rich-dobbs-13440/chromatofore/src/inchworm/filament_clamp.scad

include <ScadStoicheia/centerable.scad>
use <ScadStoicheia/visualization.scad>
include <ScadApotheka/material_colors.scad>
include <ScadApotheka/m2_helper.scad>
include <nutsnbolts-master/cyl_head_bolt.scad>
include <nutsnbolts-master/data-metric_cyl_head_bolts.scad>
use <PolyGear/PolyGear.scad>


a_lot = 200;
d_filament = 1.75 + 0.;
od_ptfe_tube = 4 + 0;
id_ptfe_tube = 2 + 0;


NEW_DEVELOPMENT = 0 + 0;
DESIGNING = 1 + 0;
MESHING_GEARS = 2 + 0;
ASSEMBLE_SUBCOMPONENTS = 3 + 0;
PRINTING = 4 + 0;



/* [Output Control] */

mode = 0; // [0:"New development, hide other parts", 1:"Designing, no rotation or translation", 2:"Meshing gears", 3: "assembly", 4: "Printing"]

function layout_from_mode(mode) = 
    mode == NEW_DEVELOPMENT ? "hidden" :
    mode == DESIGNING ? "as_designed" :
    mode == MESHING_GEARS ? "mesh_gears" :
    mode == ASSEMBLE_SUBCOMPONENTS ? "assemble" :
    mode == PRINTING ? "printing" :
    "unknown";
    
show_parts = true;
show_vitamins = true;
show_filament = true;
hide_sample_gear_keys = true;

traveller_body_visibility = 1; // [1:Solid, 0.25:Ghostly, 0:"Invisible, won't print" ]
gear_holder_visibility = 1; // [1:Solid, 0.25:Ghostly, 0:"Invisible, won't print" ]
clamp_gear_visibility = 1; // [1:Solid, 0.25:Ghostly, 0:"Invisible, won't print" ]
clamp_slot_gear_visibility = 1; // [1:Solid, 0.25:Ghostly, 0:"Invisible, won't print" ]
small_bevel_gear_visibility = 1; // [1:Solid, 0.25:Ghostly, 0:"Invisible, won't print" ]
big_bevel_gear_visibility = 1; // [1:Solid, 0.25:Ghostly, 0:"Invisible, won't print" ] 
gear_mesh_keys_visibility = 1; // [1:Solid, 0.25:Ghostly, 0:"Invisible, won't print" ]




slide_length = 50; // [1 : 1 : 99.9]
screw_lift = 0; // [-.1 : .1 : 1]

/* [Design] */

print_clearance = 0.1; // Just making it enough that Mesh tools can separate parts
x_clamp_nut_block = 7;
n_teeth_small = 9; // [9, 10, 11]




/* [Clamp Gearing Design] */
clamp_gear_height = 8;
h_bottom_clamp_gear = 1;
clamp_gear_module = 1;
ptfe_insert_clearance = 0.2;


/* [Bevel Gearing Design] */

bevel_gear_module = 1.5; //[1:0.1:2]
small_bevel_gear_cone_angle = 45; // [-90:90]
small_gear_tooth_width = 6; // [0 : 20]
dz_small_bevel_gear = 7.4; // [7:0.1: 9]
dz_shaft_small_bevel_gear = 0; // [-5:0.1:5]
h_small_bevel_shaft = 2; // [0:40]
l_bevel_shaft_bearing = 10;

flip_small_bevel_gear = false;
dz_plane_clearance_above_small_bevel = 6; // [-20 : 20]
n_teeth_big_bevel = 21; //[9 : 23]

use_mesh_keys_small_bevel = true;

/* [Slot Gearing Design] */
use_mesh_keys_slot_gear = true;
n_teeth_big_slot = 21; //[9 : 22]

/* [Gear Keying Design] */
gear_key_size = 3;
gear_key_clearance = 0.0;
gear_key_height = 4;
gear_key_displacement = 4;
gear_key_bridge_height = 0.5;
gear_key_platform_height = 2;  


module end_of_customization() {}
// Calcs for values that need to be shared to calculate displacements
id_clamp_gear = (n_teeth_small - 2) * clamp_gear_module;
od_clamp_gear  = (n_teeth_small + 2) * clamp_gear_module;
md_clamp_gear  = (n_teeth_small) * clamp_gear_module;

id_clamp_slot_gear = (n_teeth_big_slot - 2) * clamp_gear_module;
od_clamp_slot_gear = (n_teeth_big_slot + 2) * clamp_gear_module;
md_clamp_slot_gear = (n_teeth_big_slot) * clamp_gear_module;


id_small_bevel_gear = (n_teeth_small - 2) * bevel_gear_module;
od_small_bevel_gear  = (n_teeth_small + 2) * bevel_gear_module;
md_small_bevel_gear  = (n_teeth_small) * bevel_gear_module;

id_big_bevel_gear = (n_teeth_big_bevel - 2) * bevel_gear_module;
od_big_bevel_gear  = (n_teeth_big_bevel + 2) * bevel_gear_module;
md_big_bevel_gear  = (n_teeth_big_bevel) * bevel_gear_module;

overall_gear_ratio = (n_teeth_big_slot/n_teeth_small) * (n_teeth_big_bevel/n_teeth_small);

echo("Overall Gear Ratio", overall_gear_ratio);

z_traveller = md_clamp_gear/2 + od_clamp_slot_gear + l_bevel_shaft_bearing;


l_filament_to_cl_big_bevel = dz_small_bevel_gear + md_big_bevel_gear/2;

if (show_filament) {
    filament(as_clearance=false);
}

rotate_to_cl_clamp_gear = [0, 90, 0];
translate_to_cl_clamp_gear =  [
    0, 
    0, 
    -x_clamp_nut_block - clamp_gear_height/2-2]; //-14];

function filament_and_clamp_rotation() = 
    (mode == MESHING_GEARS) ? rotate_to_cl_clamp_gear : [0, 0, 0];    

function filament_and_clamp_translation() = 
    (mode == MESHING_GEARS) ? translate_to_cl_clamp_gear : [0, 0, 0];

module filament(as_clearance) {
    d = as_clearance ? 2.5 : d_filament;
    alpha = as_clearance ? 0 : 1;
    if (as_clearance) {
        can(d=d, h=slide_length + 40, $fn=12); 
    } else {
            translate(filament_and_clamp_translation() ) rotate(filament_and_clamp_rotation()) { 
            color("red", alpha) {
                can(d=d, h=slide_length + 40, $fn=12);
            }
        }
    }
    
}

layout = layout_from_mode(mode);
echo("mode", mode, "layout", layout);

gear_holder_visualization = 
    visualize_info(
        "Gear Holder", PART_1, gear_holder_visibility, layout, show_parts); 

clamp_gear_visualization = 
    visualize_info(
        "Clamp Gear", PART_2, clamp_gear_visibility, layout, show_parts);  

clamp_slot_gear_visualization = 
    visualize_info(
        "Clamp Slot Gear", PART_3, clamp_slot_gear_visibility, layout, show_parts);  

small_bevel_gear_visualization = 
    visualize_info(
        "Small Bevel Gear", PART_4, small_bevel_gear_visibility, layout, show_parts); 


big_bevel_gear_visualization = 
    visualize_info(
        "Big Bevel Gear", PART_5, big_bevel_gear_visibility, layout, show_parts); 
        
        
traveller_body_visualization  = 
    visualize_info(
        "Traveller Body", PART_6, traveller_body_visibility, layout, show_parts);       

gear_mesh_keys_visualization =
    visualize_info(
        "Gear Mess Keys", PART_30, gear_mesh_keys_visibility, layout, show_parts); 





module general_straight_spur_gear(n_teeth, gear_module, gear_height, body_child = -1, cutout_child = -1) {
    render(convexity=10) difference() {
        union() {
            spur_gear(
                n = n_teeth,  // number of teeth, just enough to clear rider.
                m = gear_module,   // module
                z = gear_height,   // thickness
                pressure_angle = 25,
                helix_angle    = 0,   // the sign gives the handiness, can be a list
                backlash       = 0.1 // in module units
            );
            if (body_child >= 0 && $children > body_child) {
                children(body_child);
            }
        }
        if (cutout_child >= 0 && $children > cutout_child) {
            children(cutout_child);
        }  
    }
}


module general_straight_spur_gear(n_teeth, gear_module, gear_height, body_child = -1, cutout_child = -1) {
    render(convexity=10) difference() {
        union() {
            spur_gear(
                n = n_teeth,  // number of teeth, just enough to clear rider.
                m = gear_module,   // module
                z = gear_height,   // thickness
                pressure_angle = 25,
                helix_angle    = 0,   // the sign gives the handiness, can be a list
                backlash       = 0.1 // in module units
            );
            if (body_child >= 0 && $children > body_child) {
                children(body_child);
            }
        }
        if (cutout_child >= 0 && $children > cutout_child) {
            children(cutout_child);
        }  
    }
}
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
